Luc3as/MySensors-WeatherStation/PCB/WeatherStation PCB.png

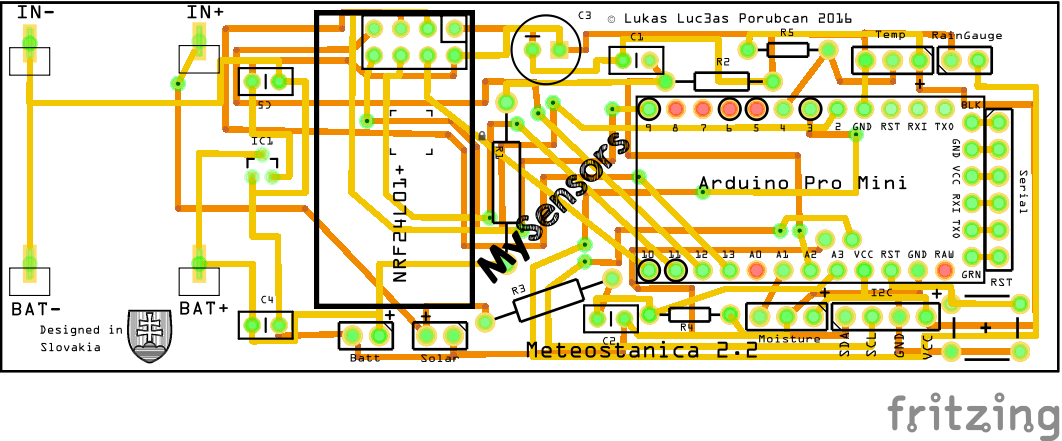
PCB/WeatherStation PCB.png
